COAST-Lab/Open-Water-Level/Data Analysis/Figures/1-year-time-series.png

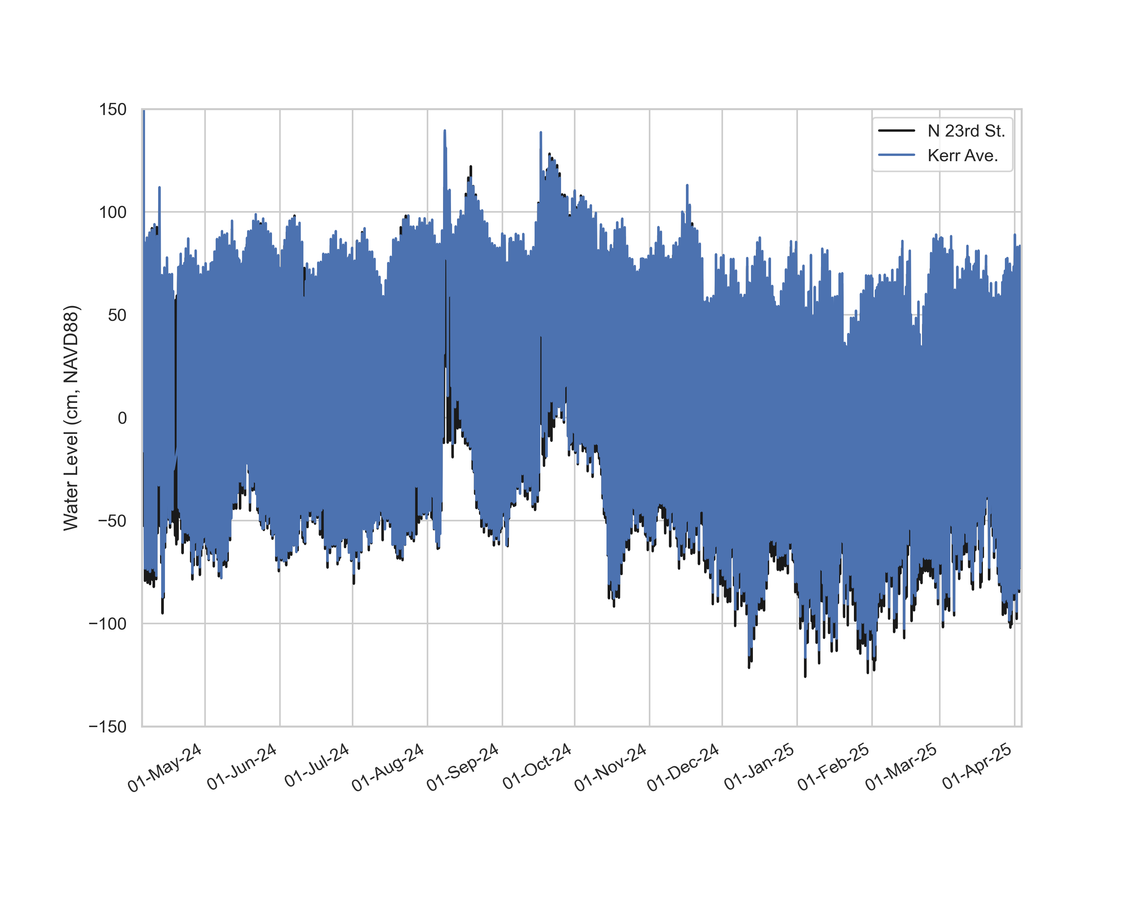
Data Analysis/Figures/1-year-time-series.png
