COAST-Lab/Open-Water-Level/Fabrication/Polycase-Enclosure/Photos/Frame_Chassis_Separate.jpeg

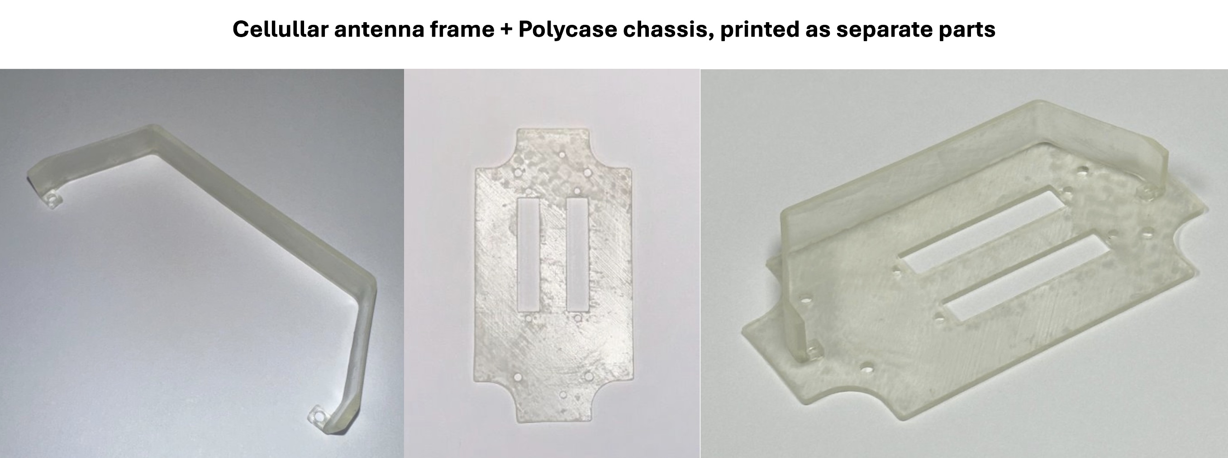
Fabrication/Polycase-Enclosure/Photos/Frame_Chassis_Separate.jpeg
