COAST-Lab/Open-Water-Level/Fabrication/Old/BOM/readme.md

# Primary Cellular BOM
See .xlsx files for similar info |  formatted in markdown for better GitHub rendering here.

Parts | URL | Cost | Function
| :---------------- | :------ | :---- | :---- |
Boron LTE CAT-M1 (NorAm) with EtherSIM (BRN404X) | https://www.digikey.com/en/products/detail/particle-industries-inc/BRN404X/17632424 | $65.31  | Microcontroller, cell modem, power management
Antenna (included in above) |  |  | Cellular communications
Cable gland for 0.08""-0.24"" Cord OD | https://www.digikey.com/en/products/detail/lapp/S2209/11200603 | $4.14  | Waterproof cable entry
MB7092 XL-MaxSonar-WRMA1 | https://www.adafruit.com/product/1137 | $99.95  | Distance sensor
Adalogger FeatherWing - RTC + SD Add-on For All Feather Boards | https://www.adafruit.com/product/2922 | $8.95  | Data storage board
Stacking header pins for FeatherWing | https://www.adafruit.com/product/2830 | $1.25  | Stack Boron on FeatherWing
SD/MicroSD Memory Card (8 GB SDHC) | https://www.adafruit.com/product/1294 | $9.95  | Data storage
Lithium Ion Battery - 3.7V 4400mAh | https://www.adafruit.com/product/354 | $19.95  | Rechargeable battery
USB DIY Slim Connector Shell - MicroB Plug | https://www.adafruit.com/product/1826 | $0.95  | Splice to solar panel power for Boron USB connection
3-pin cable | https://www.adafruit.com/product/4721 | $0.95  | Power, ground, and analog signal to/from sonar
ML-24F Outdoor NEMA Enclosure | https://www.polycase.com/ml-24f | $14.24  | Enclosure for electronics; old design: new design uses PVC pipe and 3D-printed parts
5 Watt 5 Volt 35Wh Solar System | https://voltaicsystems.com/5-watt-5-volt-35wh-solar-system/ | $99.00  | Solar charging
Loctite PL Marine Fast Cure Adhesive Sealant |  | $11.16  | Seal gland (necessary?)
FormLabs Tough Resin | https://formlabs.com/store/materials/tough-2000-resin/ | $40.00  | Mounting brackets; 1 L ($199) should suffice for ~ 5 brackets
Cell plan (we use Particle's Free Plan for now*) |  | $0.00  | Cloud data management
Total |  | $375.80  | 

Adafruit wishlist: http://www.adafruit.com/wishlists/589193  
Digi-Key wishlist: https://www.digikey.com/en/mylists/list/3G4W9NENB6
