COAST-Lab/Open-Water-Level/Fabrication/Old/Enclosure and Assembly/PVC-End-Caps/README.md

End caps designed to be 3D printed and glued (PVC cement or epoxy) onto 1-1/2" Sch 40 PVC pipe. Ultrasonic sensor is threaded into NPT threads on bottom end cap. Top end cap has bracket for fastening solar panel as well as hole for a 1.5" gripper to serve as a plug.
