COAST-Lab/Open-Water-Level/Fabrication/Old/Enclosure and Assembly/SolidWorks/README.md

Laser cut enclosure not remotely water resistant. For handheld/demo purposes only.
