COAST-Lab/Open-Water-Level/Fabrication/Polycase-Enclosure/Photos/BAda_Polycase.jpeg

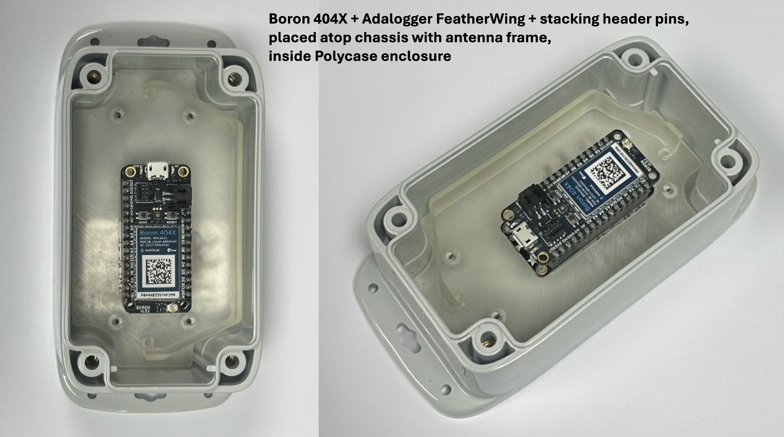
Fabrication/Polycase-Enclosure/Photos/BAda_Polycase.jpeg
