COAST-Lab/Open-Water-Level/Fabrication/Polycase-Enclosure/Photos/Maxbotix.jpeg

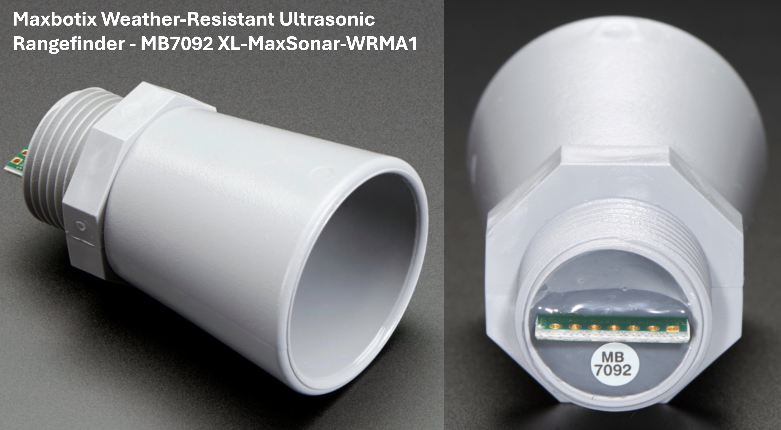
Fabrication/Polycase-Enclosure/Photos/Maxbotix.jpeg
