COAST-Lab/Open-Water-Level/Fabrication/Polycase-Enclosure/Photos/Polycase_ThreadFormingScrews.jpg

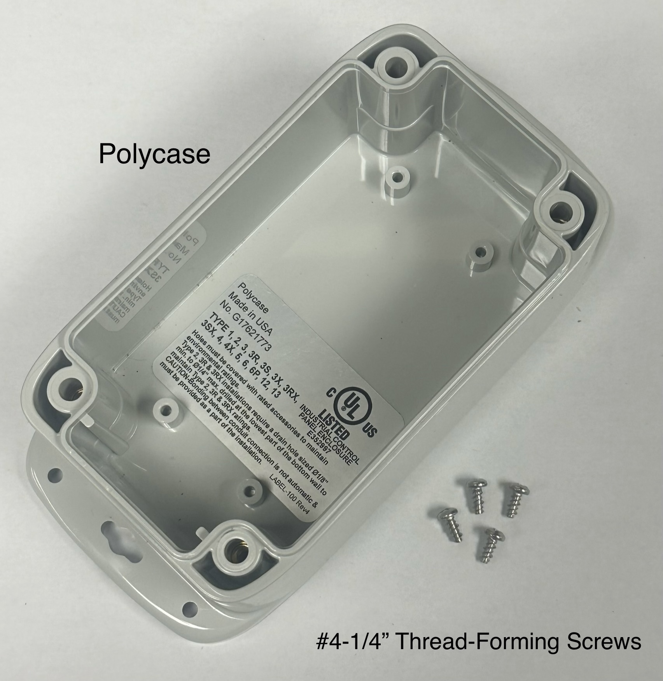
Fabrication/Polycase-Enclosure/Photos/Polycase_ThreadFormingScrews.jpg
