COAST-Lab/Open-Water-Level/Fabrication/PVC-Enclosure/Photos/BoronStack.jpeg

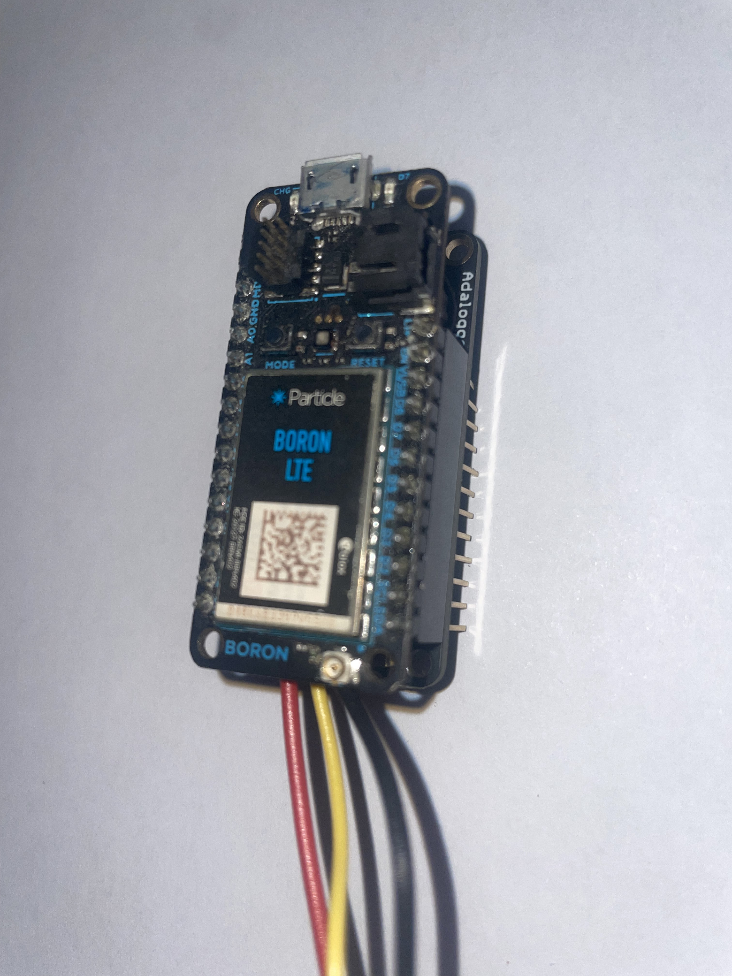
Fabrication/PVC-Enclosure/Photos/BoronStack.jpeg
