COAST-Lab/Open-Water-Level/Fabrication/Polycase-Enclosure/Enclosure-and-Assembly/20240718_Changes.png

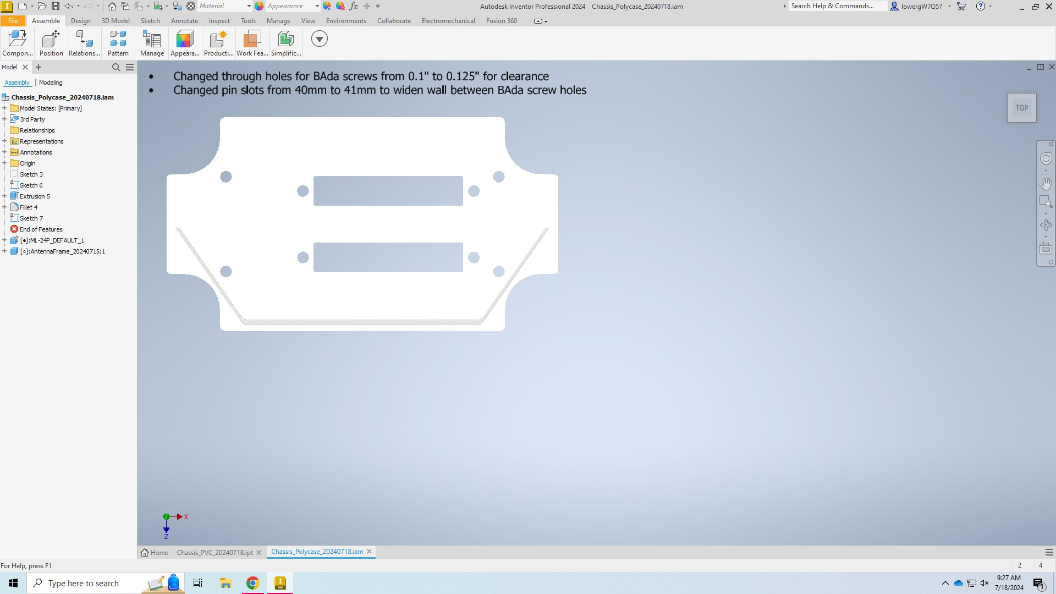
Fabrication/Polycase-Enclosure/Enclosure-and-Assembly/20240718_Changes.png
