COAST-Lab/Open-Water-Level/Fabrication/PVC-Enclosure/Enclosure-and-Assembly/20240718_Changes.png

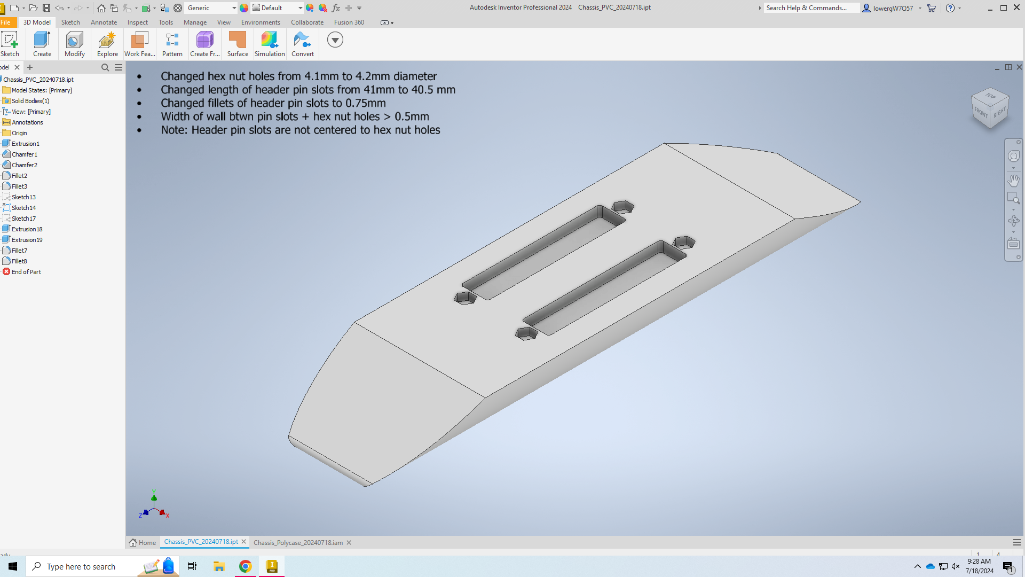
Fabrication/PVC-Enclosure/Enclosure-and-Assembly/20240718_Changes.png
